LeidyVargas/MAGIC-GLOVE/Imagenes/3d pcb/vista vacia.jpg

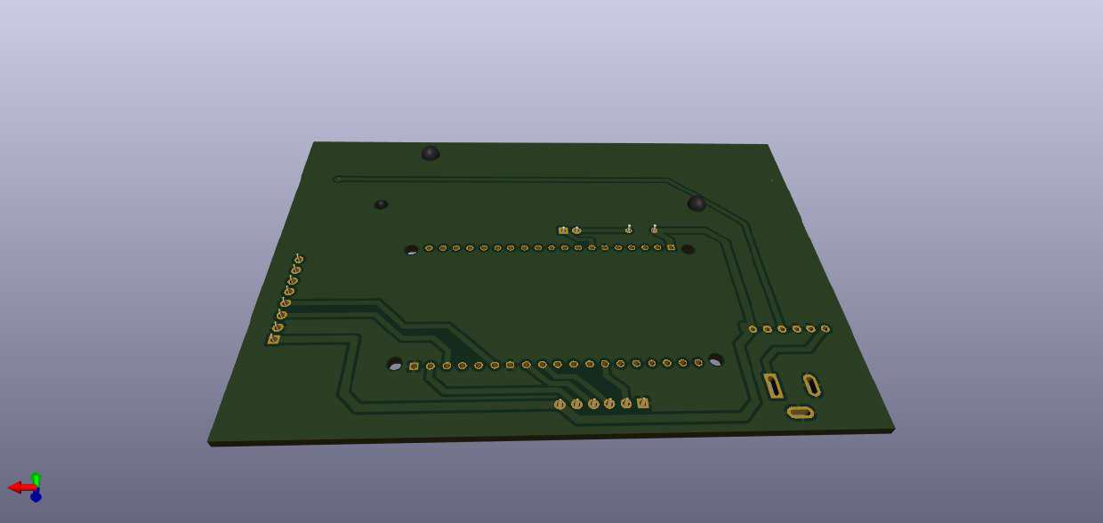
Imagenes/3d pcb/vista vacia.jpg
