LeidyVargas/MAGIC-GLOVE/Imagenes/Diagramas/DIAGRAMA CAJA NEGRA 2.png

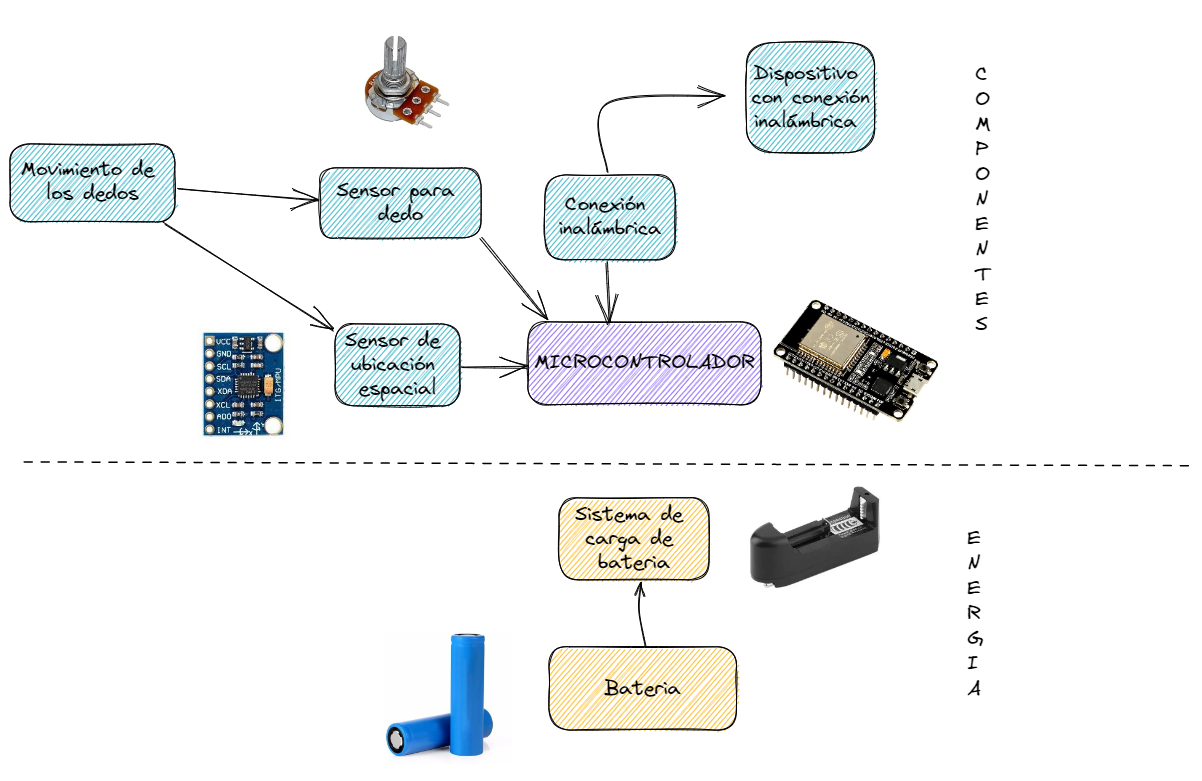
Imagenes/Diagramas/DIAGRAMA CAJA NEGRA 2.png
