LeidyVargas/MAGIC-GLOVE/Imagenes/Diagramas/DIAGRAMA DE FLUJO.png

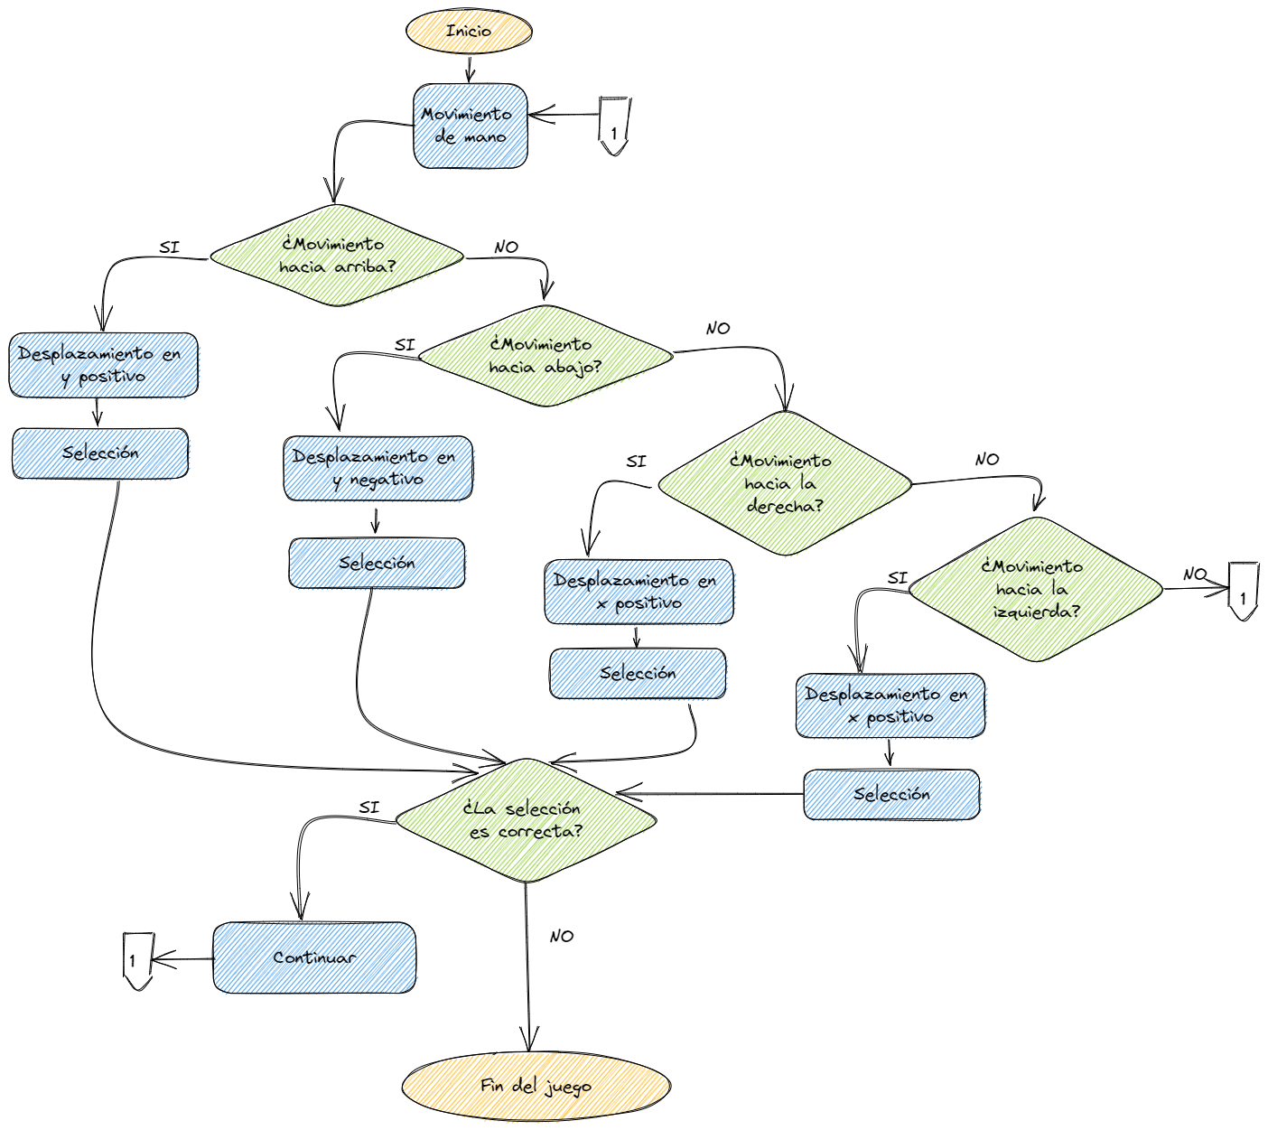
Imagenes/Diagramas/DIAGRAMA DE FLUJO.png
