LeidyVargas/MAGIC-GLOVE/Imagenes/Diagramas/ESQUEMATICO.png

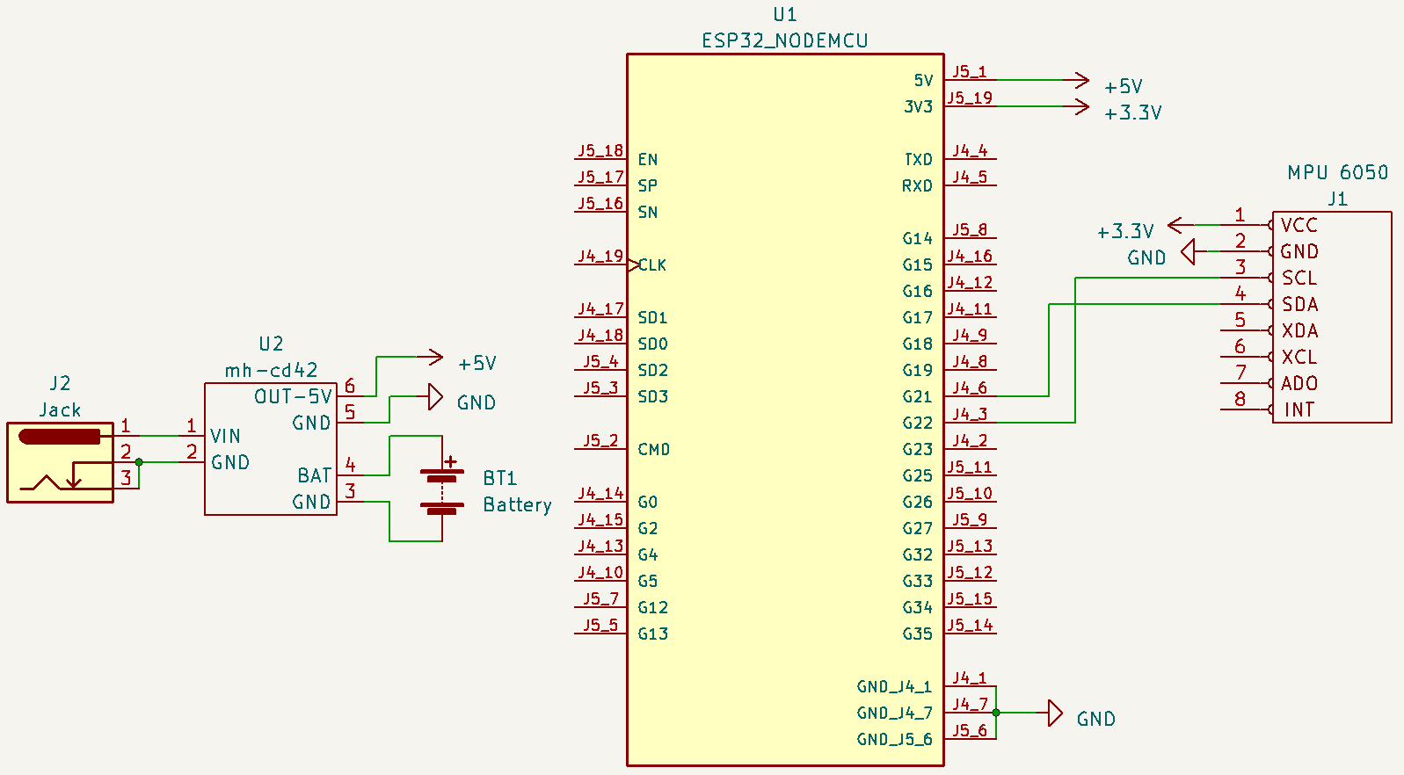
Imagenes/Diagramas/ESQUEMATICO.png
